bobjobrus/Wi-Fi-Radio-Ai-Sheff/firmware/walkie/battery.h

// Аккумулятор 18650: напряжение через делитель на АЦП, проценты, предупреждение о разряде.
// Как считается заряд и почему не сразу после включения — battery_est.h.
#pragma once

void battery_begin();
void battery_loop();        // из loop(): замер раз в секунду
