bobjobrus/Wi-Fi-Radio-Ai-Sheff/firmware/walkie/web.h

// Страница рации: состояние, Wi-Fi, настройки, обновление прошивки файлом.
// Открывается по адресу рации в сети (http://radio-xxxx.local/) или в режиме настройки — http://192.168.4.1/
#pragma once

void web_begin();
void web_loop();
